EdYazbec/MotorCityField/2025 Specific/TE-25100/TE-25100.SLDASM

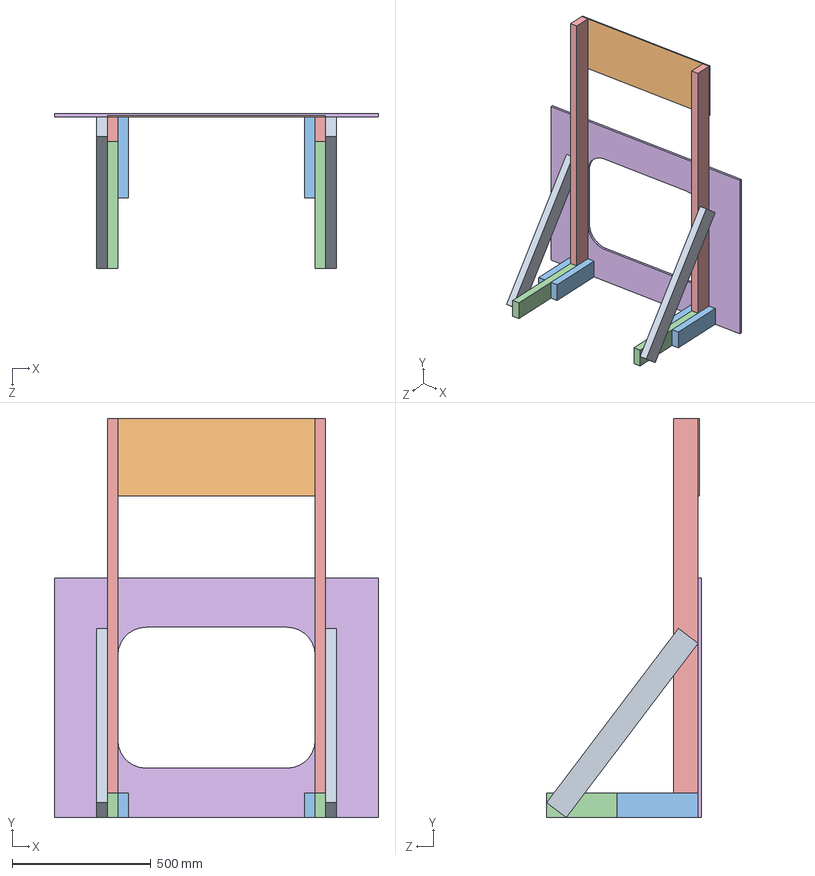
[picture p19: CAD file, 2025-06-08]
2025 Specific/TE-25100/TE-25100.SLDASM
1168.4 x 1438.3 x 558.0 mm
TE-25101
TE-25102 x 2
TE-25103 x 2
TE-25105 x 4
TE-25106
TE-25104 x 2
