EdYazbec/MotorCityField/Perimeter/Gate Segment/Gate Segment.SLDASM

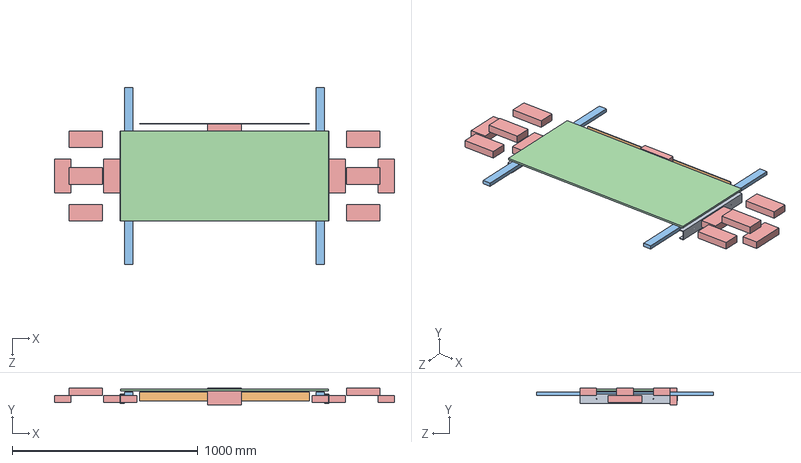
[picture p20: CAD file, 2025-06-08]
Perimeter/Gate Segment/Gate Segment.SLDASM
1828.8 x 88.9 x 952.5 mm
2x4 x 13
Gate Door Pannel
1x2 x 2
2in Hook Tape
u channel x 2
