EdYazbec/MotorCityField/Driver Station Wall/Driver Station/Driver Station.SLDASM

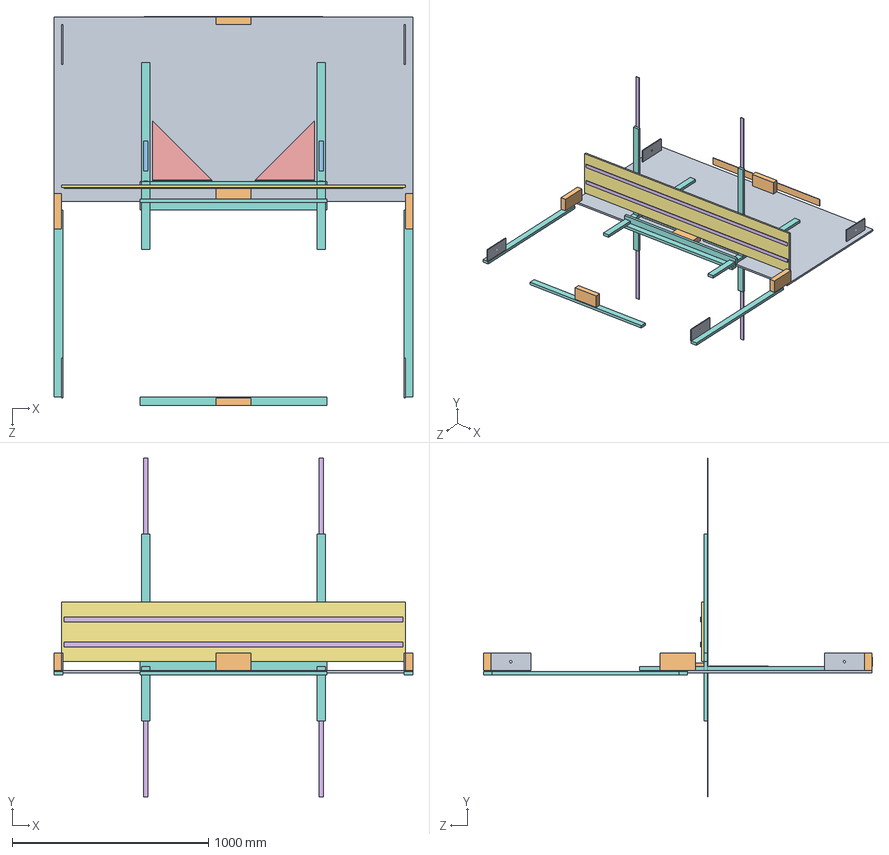
[picture p21: CAD file, 2025-06-08]
Driver Station Wall/Driver Station/Driver Station.SLDASM
1828.8 x 1727.2 x 1984.4 mm
2x4 x 5
DS Wall Plate
1x2 x 10
DS Shelf Slab
1in Hook Tape x 4
DS Shelf Support x 2
0.5in Loop Tape x 2
1in Loop Tape x 2
2in Hook Tape
DS Spacer x 4
