EdYazbec/MotorCityField/Driver Station Wall/Driver Station/DS Shelf.SLDASM

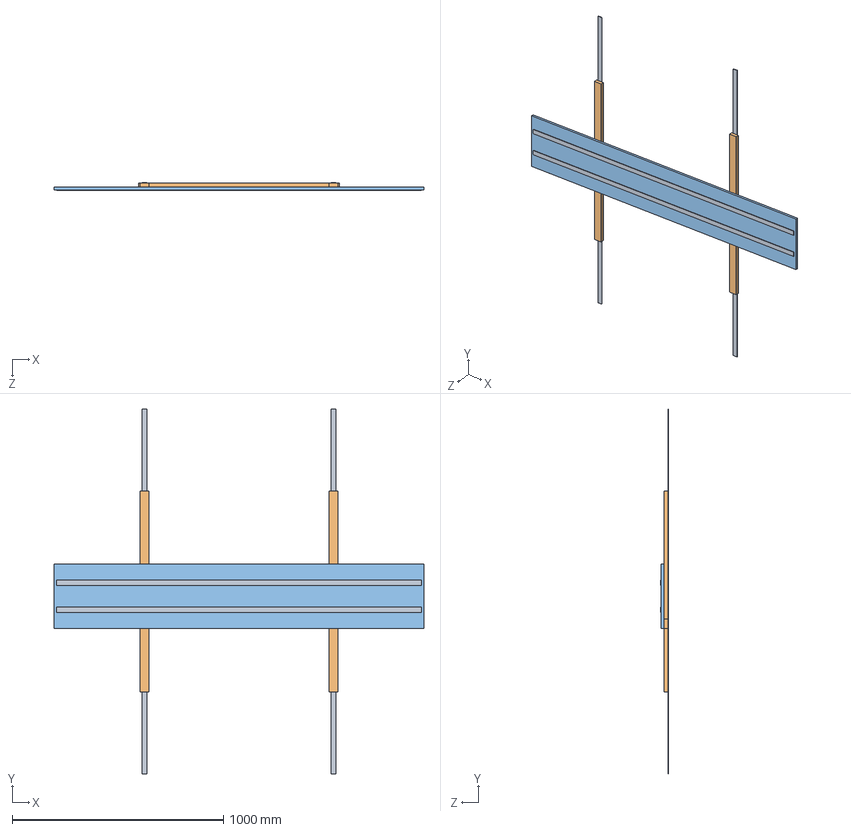
[picture p22: CAD file, 2025-06-08]
Driver Station Wall/Driver Station/DS Shelf.SLDASM
1752.6 x 1727.2 x 38.1 mm
DS Shelf Slab
1x2 x 3
1in Hook Tape x 4
