EdYazbec/MotorCityField/2025 Specific/TE-25100/TE-25103.SLDPRT

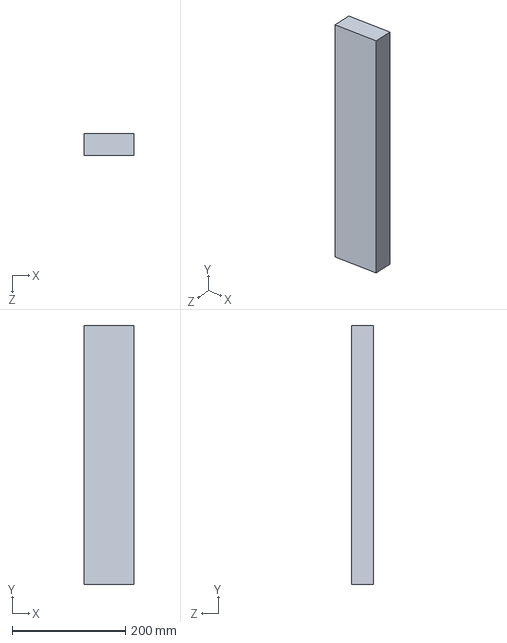
[picture p26: CAD file, 2025-06-08]
2025 Specific/TE-25100/TE-25103.SLDPRT
88.9 x 457.2 x 38.1 mm
