EdYazbec/MotorCityField/Common/1in Loop Tape.SLDPRT

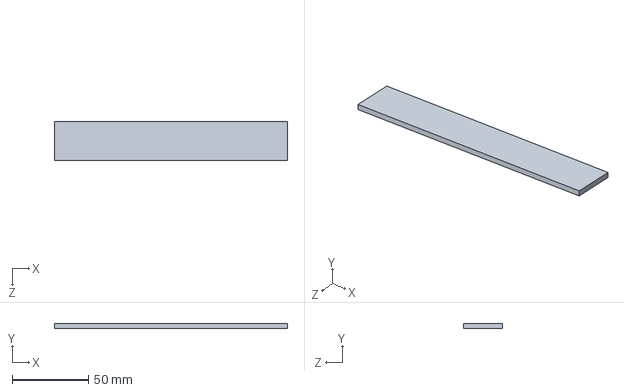
[picture p27: CAD file, 2025-06-08]
Common/1in Loop Tape.SLDPRT
152.4 x 3.17 x 25.4 mm
