EdYazbec/MotorCityField/Driver Station Wall/Driver Station Bace/DS Brace Bottom Fin.SLDPRT

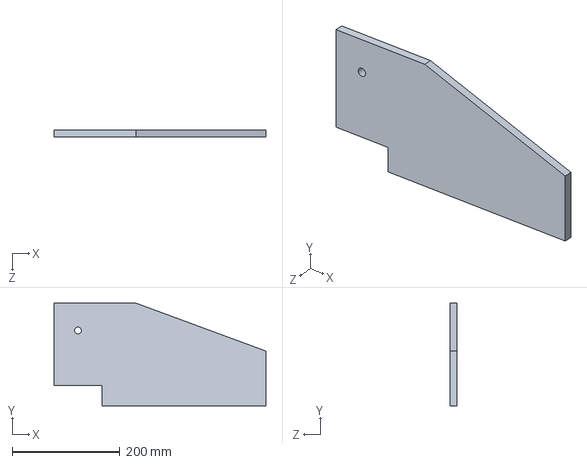
[picture p28: CAD file, 2025-06-08]
Driver Station Wall/Driver Station Bace/DS Brace Bottom Fin.SLDPRT
393.7 x 190.5 x 12.7 mm
