EdYazbec/MotorCityField/Perimeter/Gate Segment/Gate Door Pannel.SLDPRT

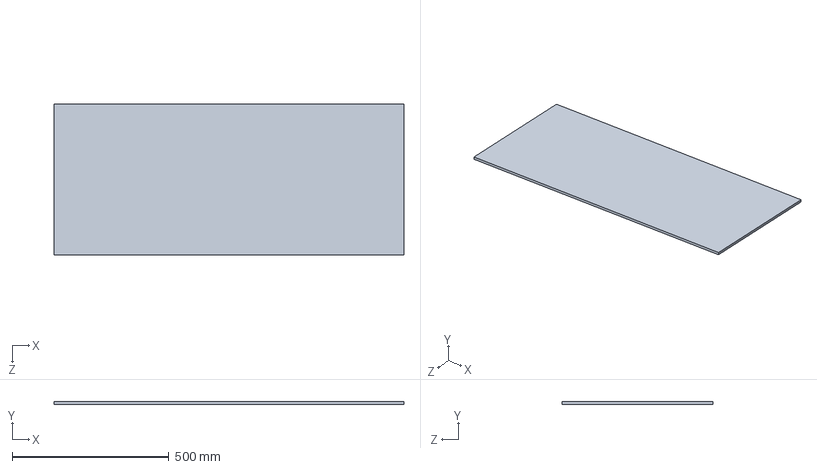
[picture p29: CAD file, 2025-06-08]
Perimeter/Gate Segment/Gate Door Pannel.SLDPRT
1117.6 x 9.53 x 482.6 mm
