EdYazbec/MotorCityField/Perimeter/Perimeter Brace/Wall gusset.SLDPRT

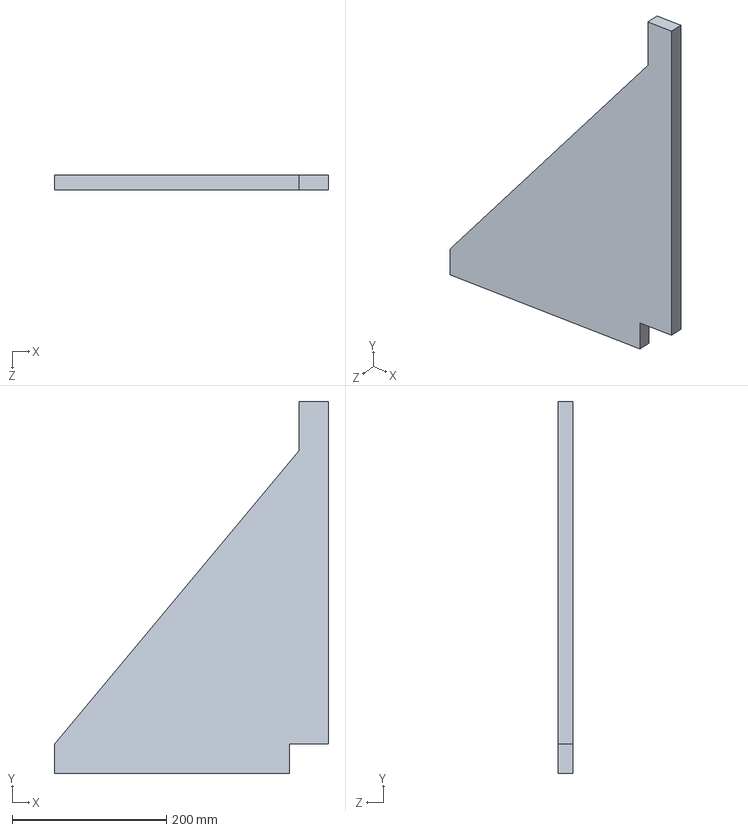
[picture p30: CAD file, 2025-06-08]
Perimeter/Perimeter Brace/Wall gusset.SLDPRT
355.6 x 482.6 x 19.1 mm
