EdYazbec/MotorCityField/2025 Specific/TE-25100/TE-25105.SLDPRT

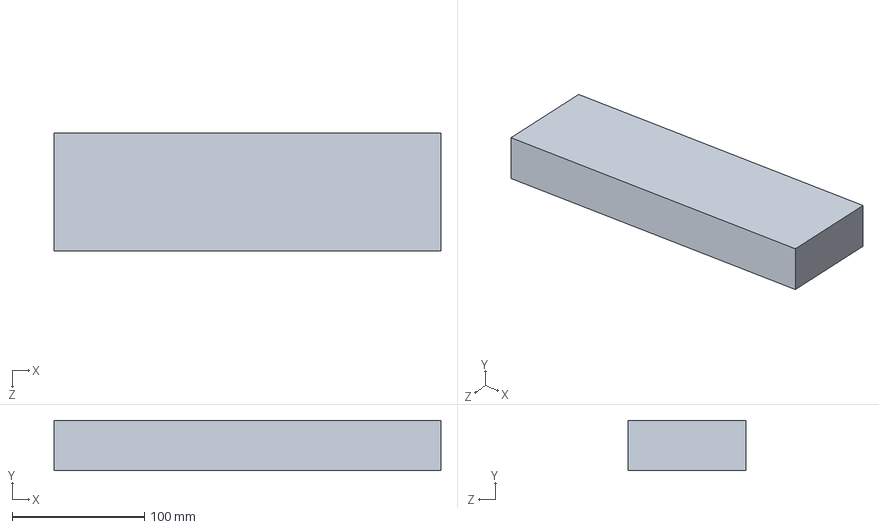
[picture p31: CAD file, 2025-06-08]
2025 Specific/TE-25100/TE-25105.SLDPRT
292.1 x 38.1 x 88.9 mm
