EdYazbec/MotorCityField/Common/0.5in Loop Tape.SLDPRT

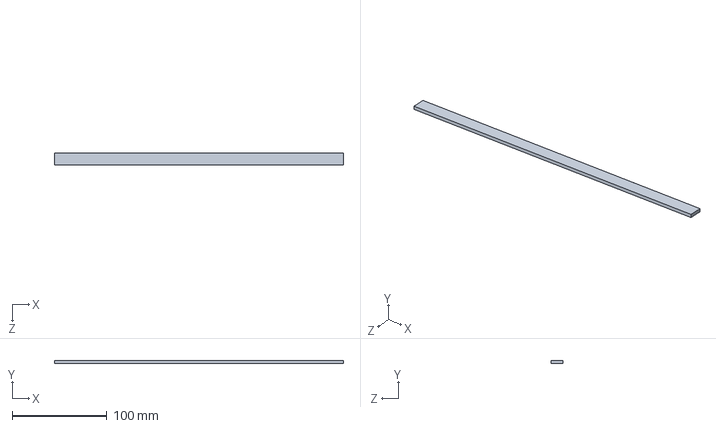
[picture p32: CAD file, 2025-06-08]
Common/0.5in Loop Tape.SLDPRT
304.8 x 3.17 x 12.7 mm
