EdYazbec/MotorCityField/Driver Station Wall/Driver Station Bace/DS Brace Top Fin.SLDPRT

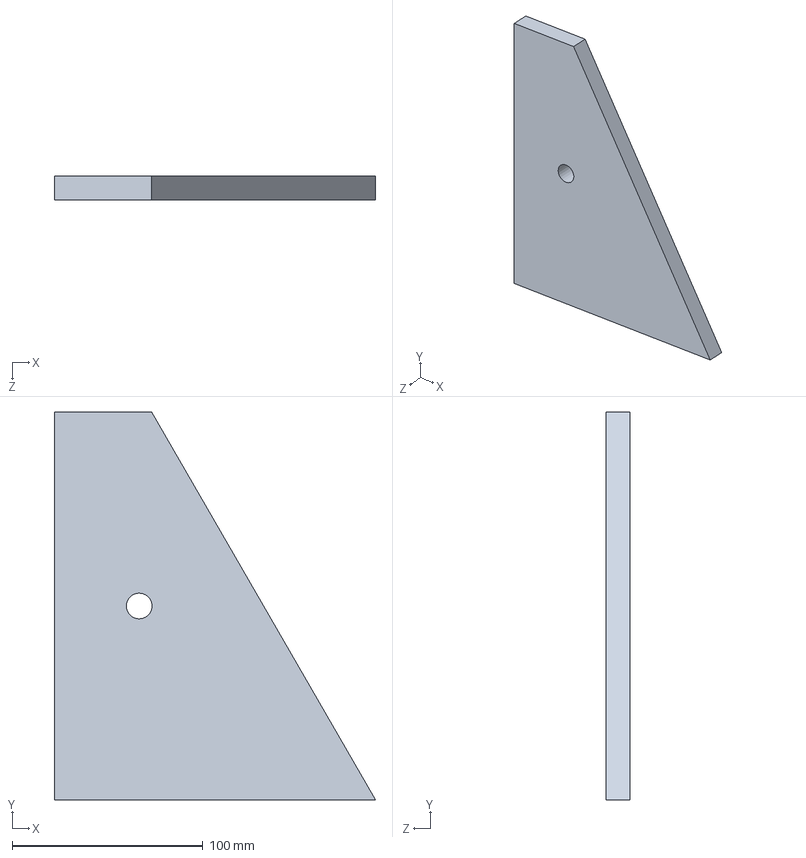
[picture p33: CAD file, 2025-06-08]
Driver Station Wall/Driver Station Bace/DS Brace Top Fin.SLDPRT
168.3 x 203.2 x 12.7 mm
