EdYazbec/MotorCityField/Driver Station Wall/Driver Station/DS Spacer.SLDPRT

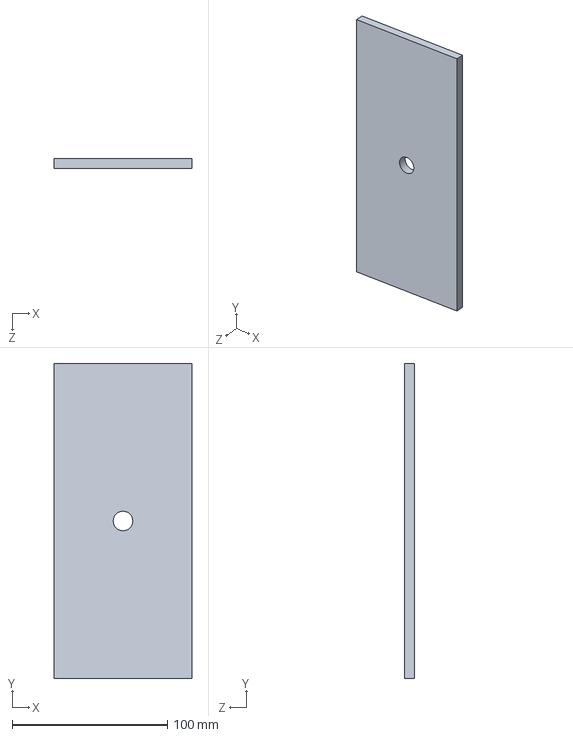
[picture p34: CAD file, 2025-06-08]
Driver Station Wall/Driver Station/DS Spacer.SLDPRT
88.9 x 203.2 x 6.35 mm
