EdYazbec/MotorCityField/Perimeter/Gate Segment/u channel.SLDPRT

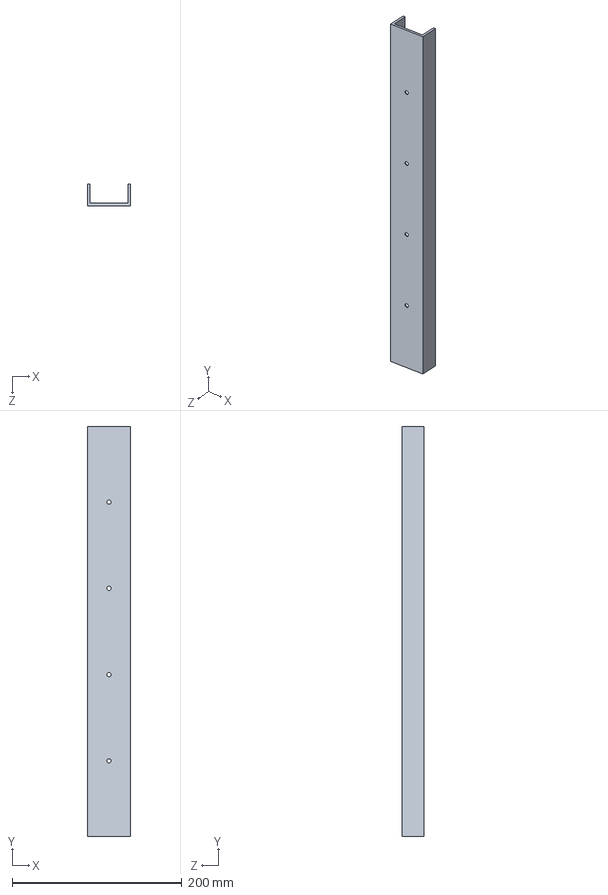
[picture p35: CAD file, 2025-06-08]
Perimeter/Gate Segment/u channel.SLDPRT
50.8 x 482.6 x 25.4 mm
