EdYazbec/MotorCityField/Common/2x4.SLDPRT

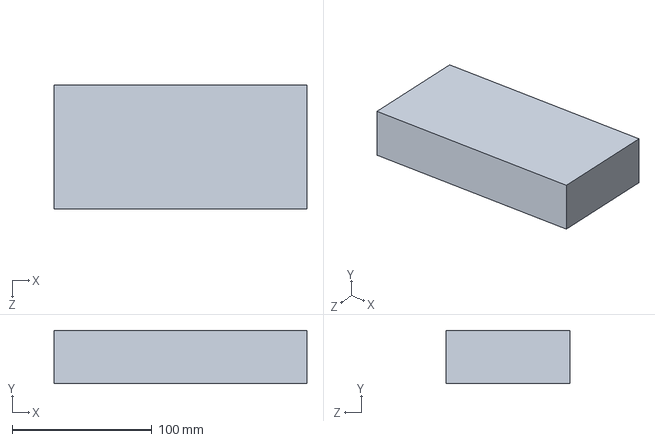
[picture p36: CAD file, 2025-06-08]
Common/2x4.SLDPRT
181.0 x 38.1 x 88.9 mm
