EdYazbec/MotorCityField/Driver Station Wall/Driver Station Bace/2x4 DS angled piece.SLDPRT

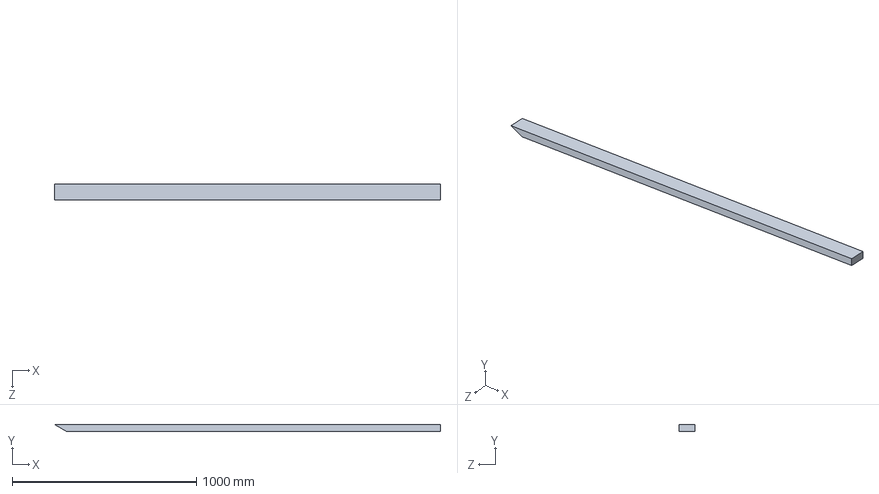
[picture p37: CAD file, 2025-06-08]
Driver Station Wall/Driver Station Bace/2x4 DS angled piece.SLDPRT
2095.5 x 38.1 x 88.9 mm
