EdYazbec/MotorCityField/Driver Station Wall/Driver Station/DS Shelf Support.SLDPRT

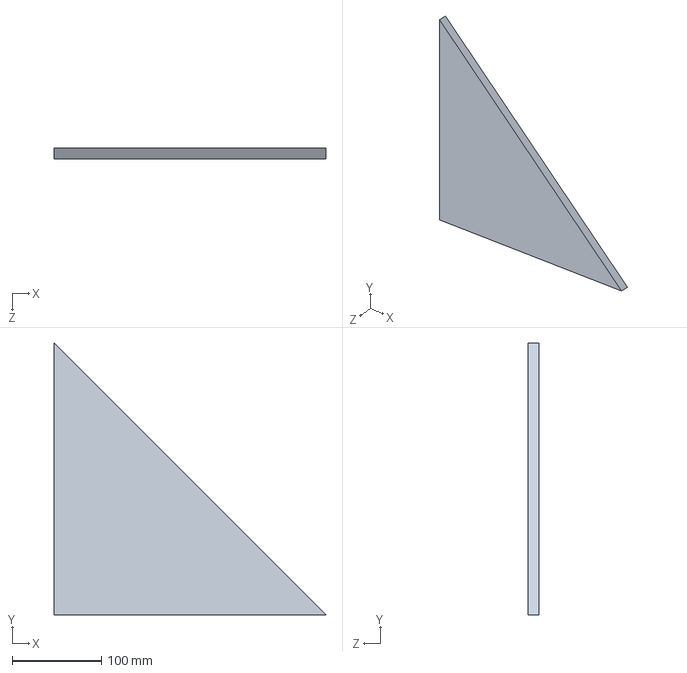
[picture p38: CAD file, 2025-06-08]
Driver Station Wall/Driver Station/DS Shelf Support.SLDPRT
304.8 x 304.8 x 12.7 mm
