EdYazbec/MotorCityField/2025 Specific/TE-25100/TE-25101.SLDPRT

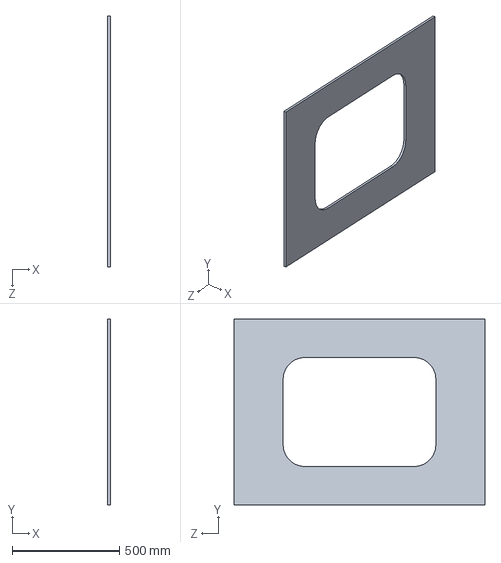
[picture p39: CAD file, 2025-06-08]
2025 Specific/TE-25100/TE-25101.SLDPRT
11.9 x 863.6 x 1168.4 mm
