EdYazbec/MotorCityField/Common/2in Hook Tape.SLDPRT

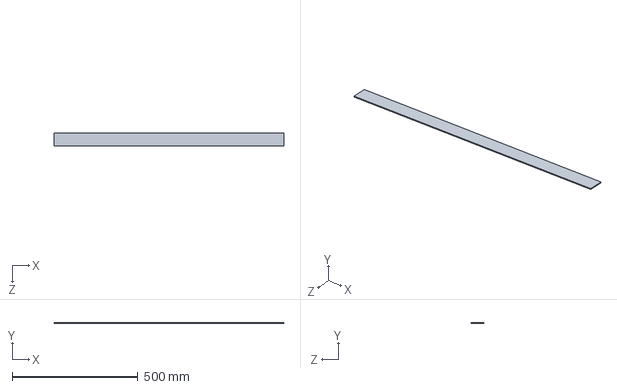
[picture p40: CAD file, 2025-06-08]
Common/2in Hook Tape.SLDPRT
914.4 x 3.17 x 50.8 mm
