EdYazbec/MotorCityField/Driver Station Wall/Driver Station/DS Wall Wedge.SLDPRT

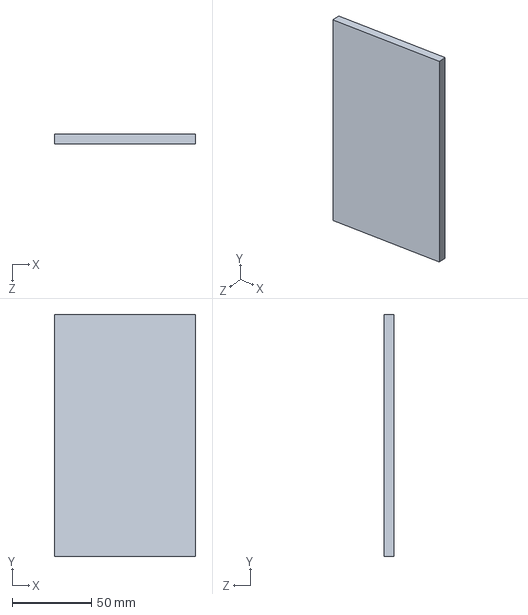
[picture p41: CAD file, 2025-06-08]
Driver Station Wall/Driver Station/DS Wall Wedge.SLDPRT
88.9 x 152.4 x 6.35 mm
