EdYazbec/MotorCityField/2025 Specific/TE-25100/TE-25102.SLDPRT

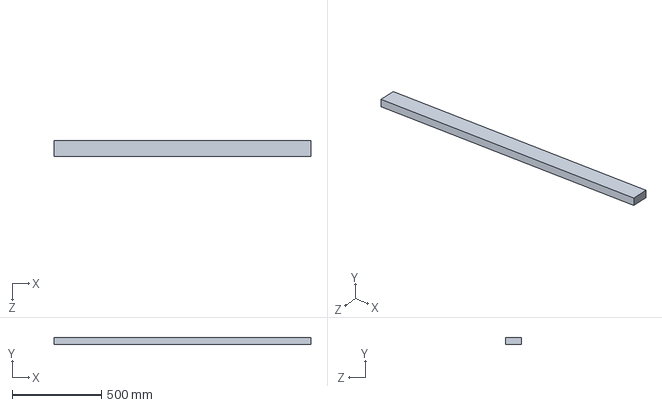
[picture p42: CAD file, 2025-06-08]
2025 Specific/TE-25100/TE-25102.SLDPRT
1438.3 x 38.1 x 88.9 mm
