EdYazbec/MotorCityField/Common/1x2.SLDPRT

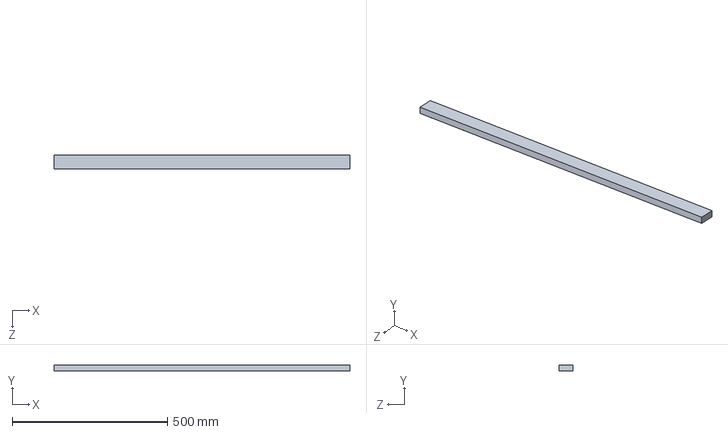
[picture p43: CAD file, 2025-06-08]
Common/1x2.SLDPRT
952.5 x 19.1 x 44.5 mm
