EdYazbec/MotorCityField/2025 Specific/TE-25100/TE-25104.SLDPRT

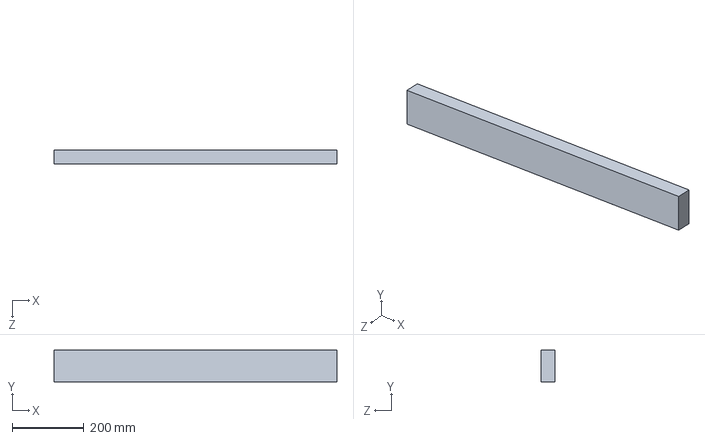
[picture p44: CAD file, 2025-06-08]
2025 Specific/TE-25100/TE-25104.SLDPRT
787.4 x 88.9 x 38.1 mm
