EdYazbec/MotorCityField/Driver Station Wall/Driver Station/DS Wall Plate.SLDPRT

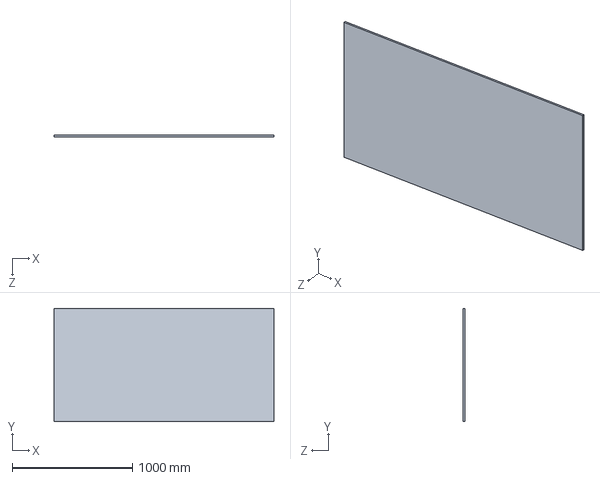
[picture p45: CAD file, 2025-06-08]
Driver Station Wall/Driver Station/DS Wall Plate.SLDPRT
1828.8 x 939.8 x 12.7 mm
