EdYazbec/MotorCityField/Driver Station Wall/Driver Station/DS Shelf Slab.SLDPRT

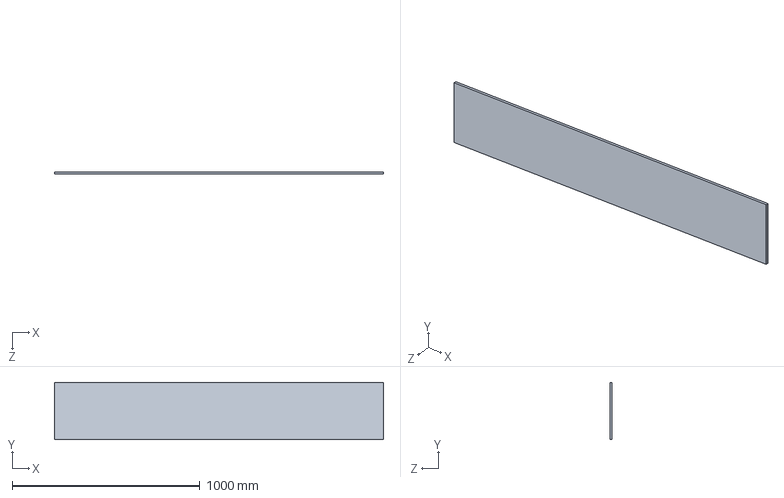
[picture p46: CAD file, 2025-06-08]
Driver Station Wall/Driver Station/DS Shelf Slab.SLDPRT
1752.6 x 304.8 x 12.7 mm
