EdYazbec/MotorCityField/Drawing Package/Driver Station Wall/Driver Station/DS Shelf Support LH.pdf

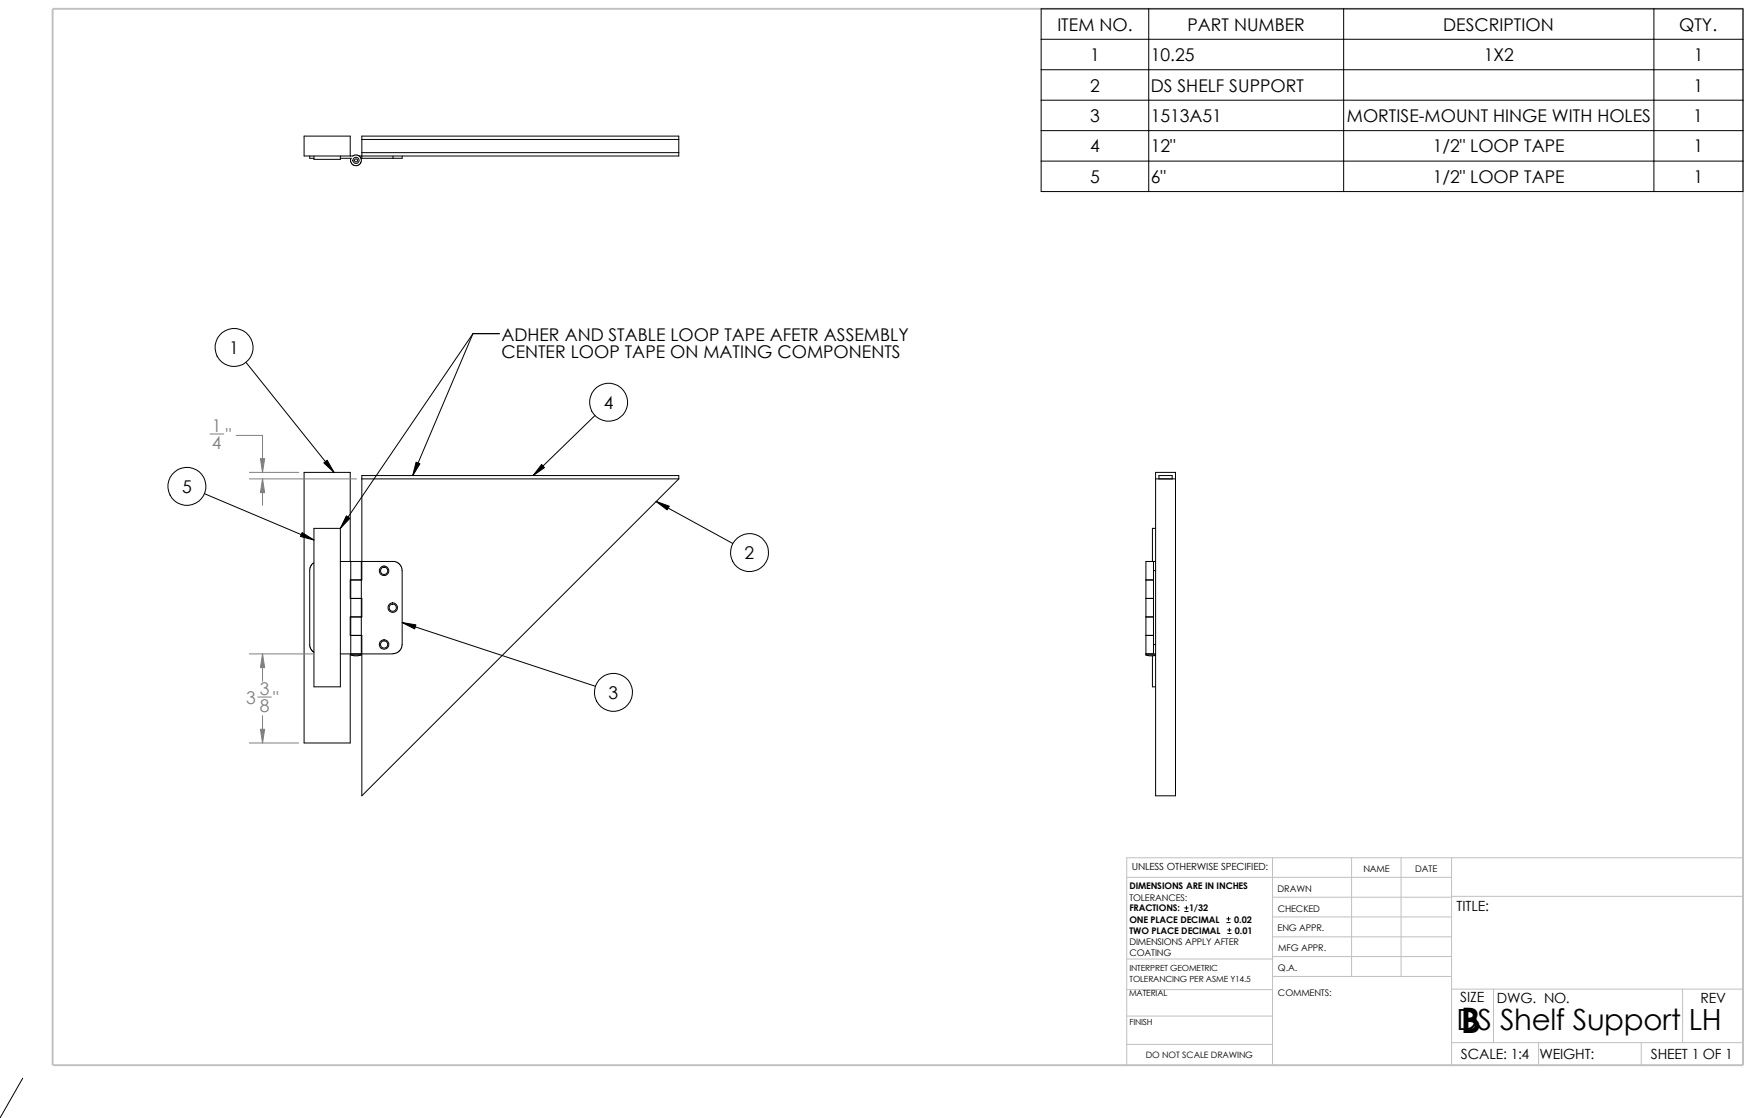
[picture p57: page 1]
COMMENTS:; DWG. NO.; REV; SCALE: 1:4; WEIGHT:; SIZE; FINISH; DS Shelf Support LH B; MATERIAL; SHEET 1 OF 1

ITEM NO. | PART NUMBER | DESCRIPTION | QTY.
1 | 10.25 | 1X2 | 1
2 | DS SHELF SUPPORT | | 1
3 | 1513A51 | MORTISE-MOUNT HINGE WITH HOLES | 1
4 | 12" | 1/2" LOOP TAPE | 1
5 | 6" | 1/2" LOOP TAPE | 1

ADHER AND STABLE LOOP TAPE AFETR ASSEMBLY
CENTER LOOP TAPE ON MATING COMPONENTS

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

CHECKED | | | TITLE:

ENG APPR.
MFG APPR.

INTERPRET GEOMETRIC TOLERANCING PER ASME Y14.5 | Q.A.

DO NOT SCALE DRAWING
