EdYazbec/MotorCityField/Drawing Package/Driver Station Wall/Driver Station/DS Shelf.pdf

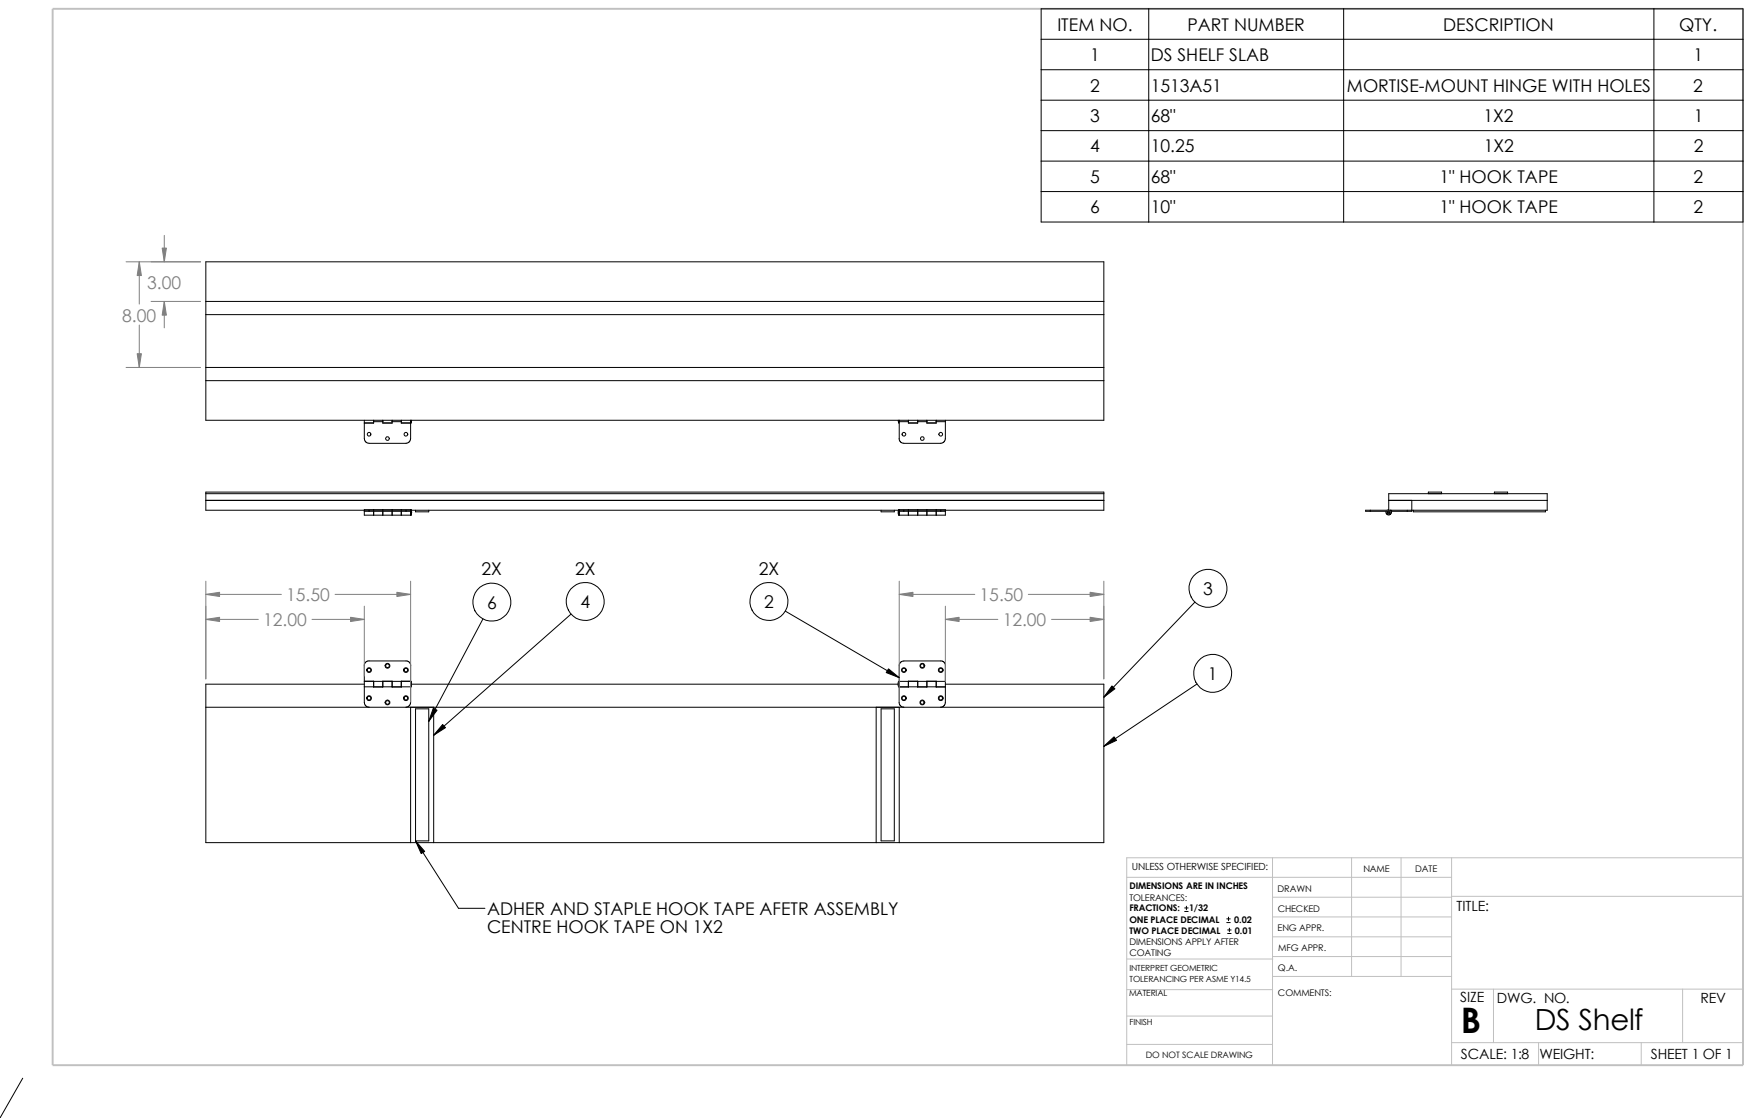
[picture p58: page 1]
COMMENTS:; DS Shelf; REV; WEIGHT:; SIZE; DWG. NO.; SCALE: 1:8; FINISH; MATERIAL; SHEET 1 OF 1

ITEM NO. | PART NUMBER | DESCRIPTION | QTY.
1 | DS SHELF SLAB | | 1
2 | 1513A51 | MORTISE-MOUNT HINGE WITH HOLES | 2
3 | 68" | 1X2 | 1
4 | 10.25 | 1X2 | 2
5 | 68" | 1" HOOK TAPE | 2
6 | 10" | 1" HOOK TAPE | 2

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

ADHER AND STAPLE HOOK TAPE AFETR ASSEMBLY
CENTRE HOOK TAPE ON 1X2

CHECKED | | | TITLE:

ENG APPR.
MFG APPR.

INTERPRET GEOMETRIC TOLERANCING PER ASME Y14.5 | Q.A.

DO NOT SCALE DRAWING
