EdYazbec/MotorCityField/Drawing Package/Driver Station Wall/Driver Station/DS Spacer.pdf

1
4

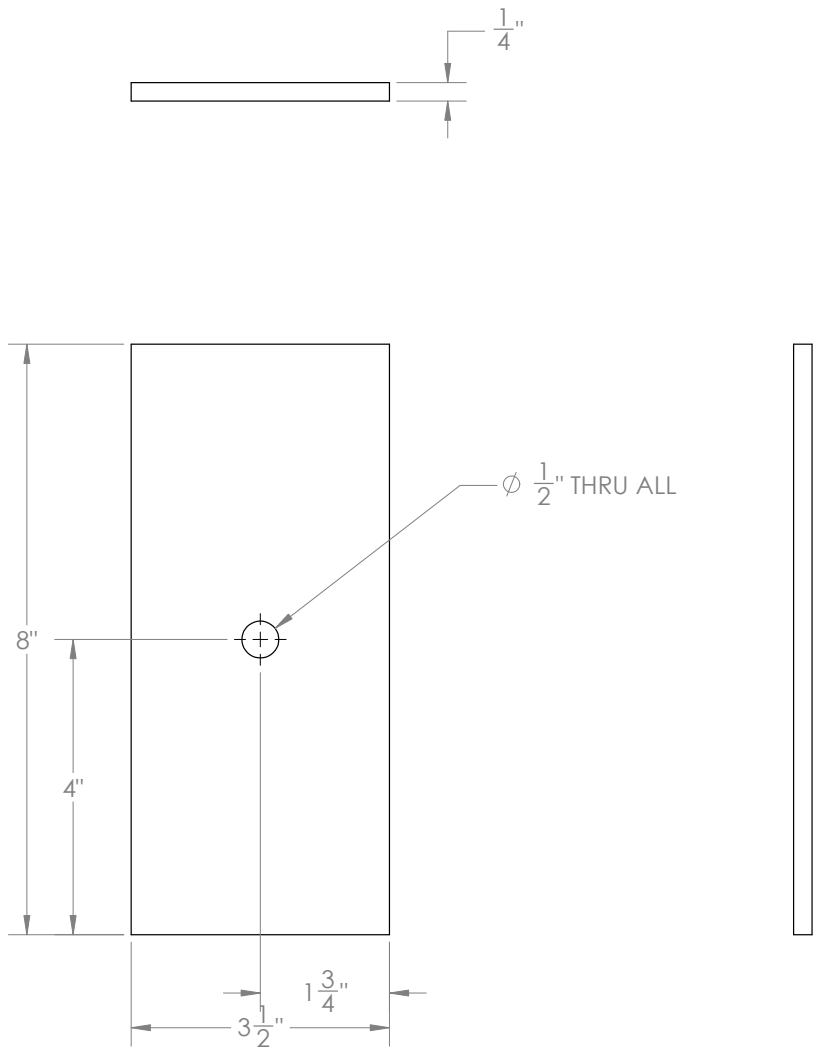
[picture p59: page 1]
SIZE; REV; COMMENTS:; DS Spacer; FINISH; SHEET 1 OF 1; SCALE: 1:2; WEIGHT:; " THRU ALL

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

CHECKED | | | TITLE:

ENG APPR.
MFG APPR.

INTERPRET GEOMETRIC TOLERANCING PER ASME Y14.5 | Q.A.

MATERIAL
DWG. NO. 1/4" PLYWOOD

DO NOT SCALE DRAWING
