EdYazbec/MotorCityField/Drawing Package/Driver Station Wall/Driver Station/DS Wall Plate.pdf

.50

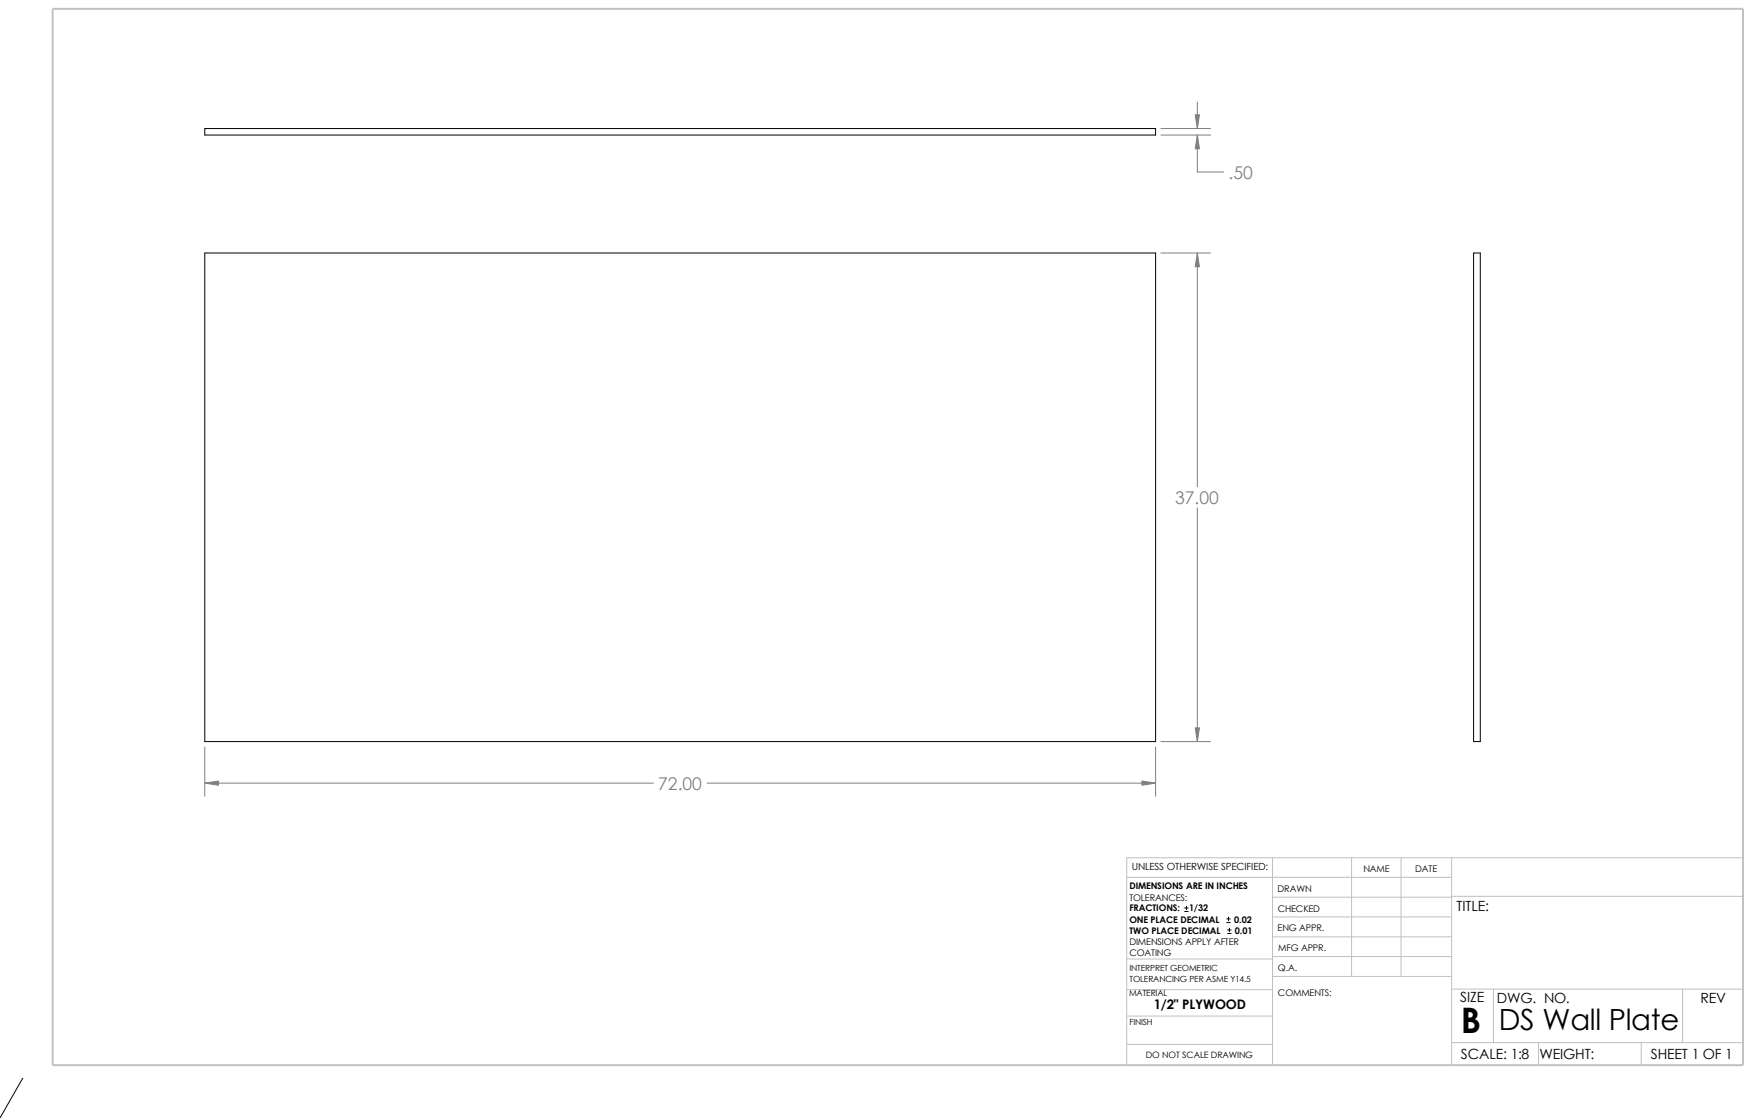
[picture p60: page 1]
SIZE; REV; COMMENTS:; FINISH; SHEET 1 OF 1; SCALE: 1:8; WEIGHT:

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

CHECKED | | | TITLE:

ENG APPR.
MFG APPR.

INTERPRET GEOMETRIC TOLERANCING PER ASME Y14.5 | Q.A.

MATERIAL
DWG. NO. 1/2" PLYWOOD

DS Wall Plate

DO NOT SCALE DRAWING
