EdYazbec/MotorCityField/Drawing Package/Perimeter/Gate Segment/Gate Door.pdf

2 2X

3 2X | ITEM NO. | PART / LENGTH | MATERIAL | QTY.

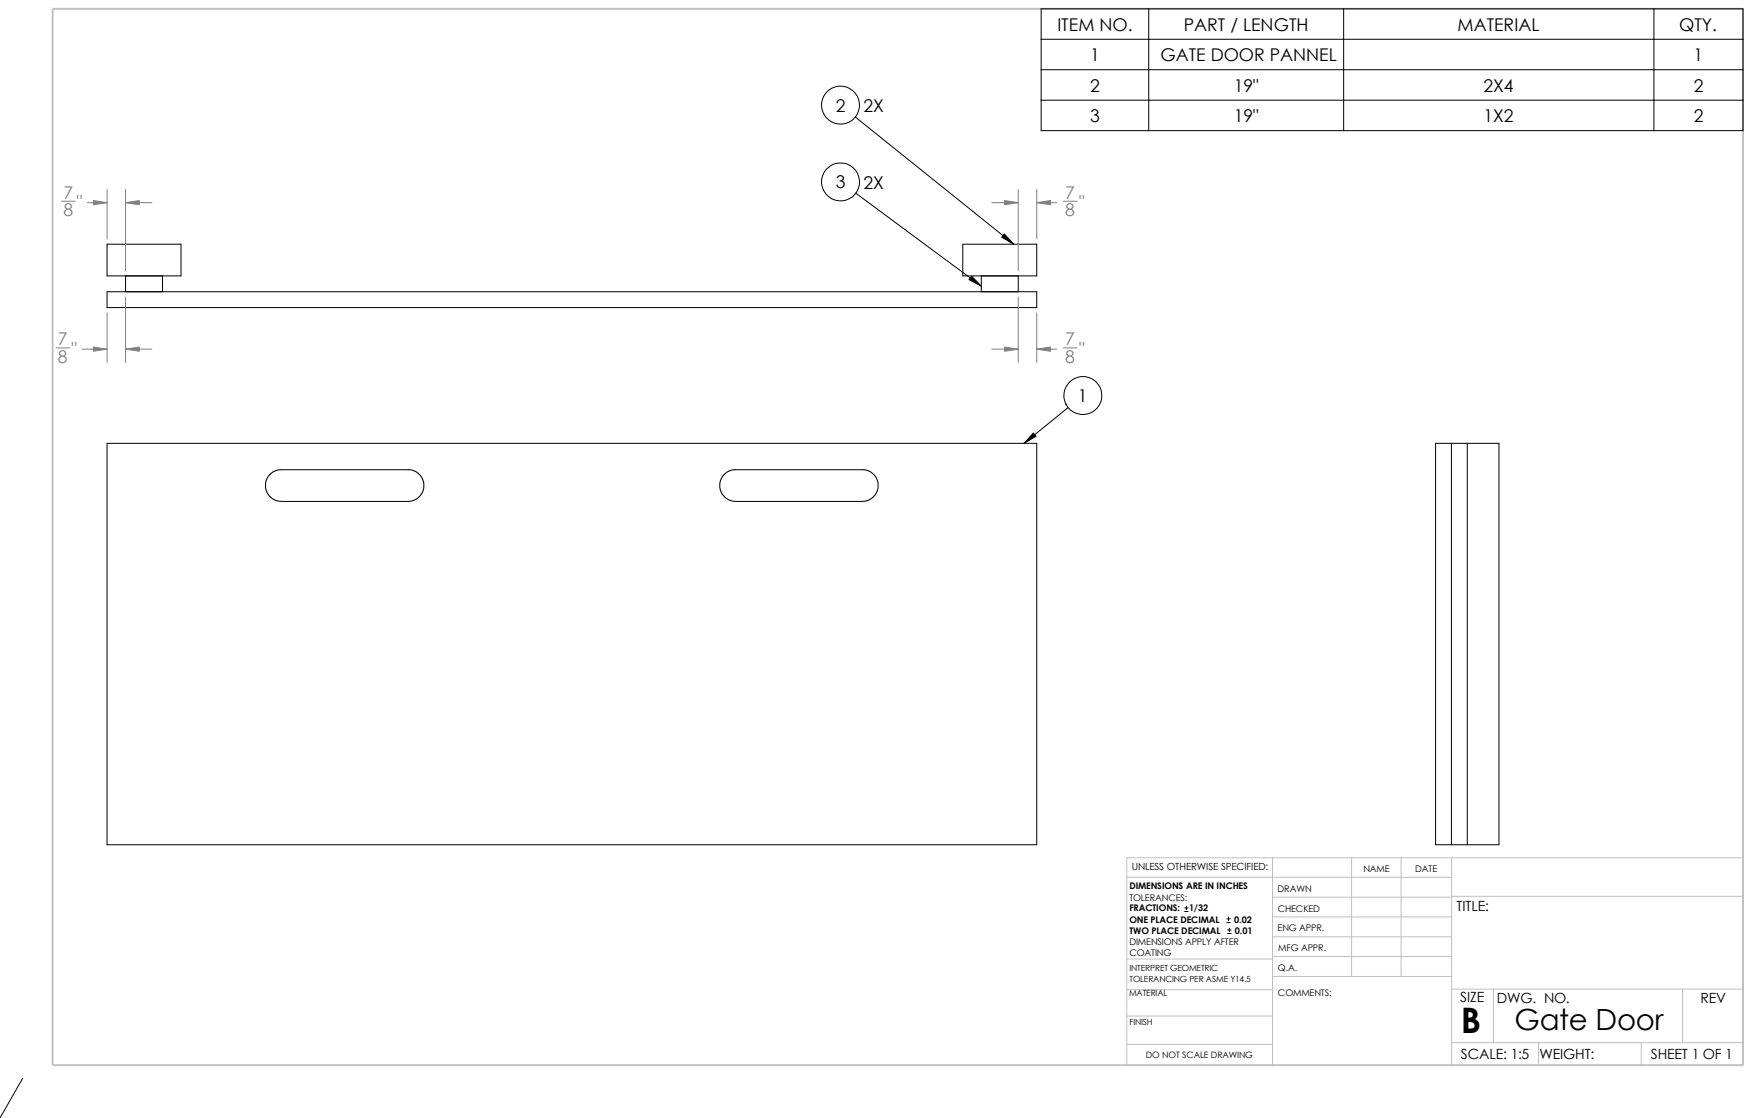
[picture p61: page 1]
COMMENTS:; DWG. NO.; REV; SCALE: 1:5; WEIGHT:; SIZE; SHEET 1 OF 1

1 | GATE DOOR PANNEL | | 1
2 | 19" | 2X4 | 2
3 | 19" | 1X2 | 2

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

CHECKED | | | TITLE:

ENG APPR.
MFG APPR.

INTERPRET GEOMETRIC TOLERANCING PER ASME Y14.5 | Q.A.

MATERIAL
B Gate Door FINISH

DO NOT SCALE DRAWING
