EdYazbec/MotorCityField/Drawing Package/Perimeter/Gate Segment/Gate Segment.pdf

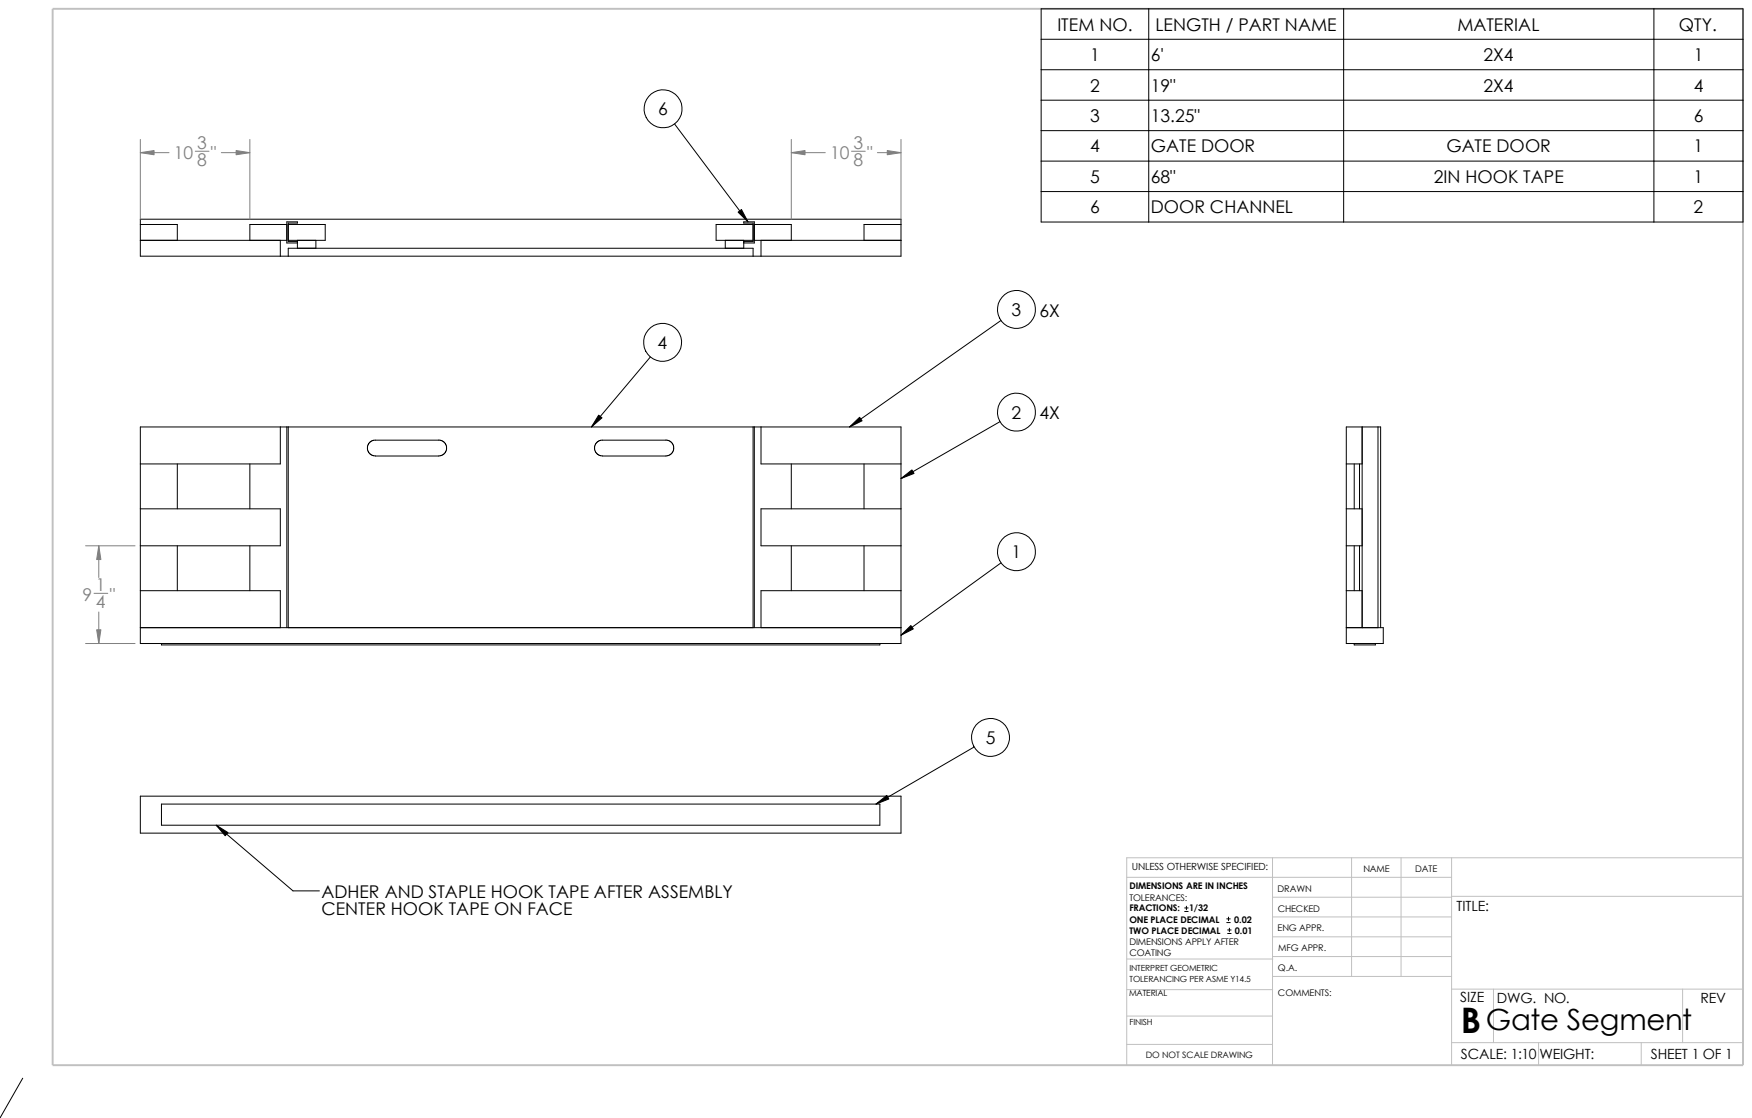
[picture p62: page 1]
COMMENTS:; DWG. NO.; REV; SCALE: 1:10 WEIGHT:; SIZE; SHEET 1 OF 1

6 | ITEM NO. | LENGTH / PART NAME | MATERIAL | QTY.

1 | 6' | 2X4 | 1
2 | 19" | 2X4 | 4
3 | 13.25" | | 6
4 | GATE DOOR | GATE DOOR | 1
5 | 68" | 2IN HOOK TAPE | 1
6 | DOOR CHANNEL | | 2

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

ADHER AND STAPLE HOOK TAPE AFTER ASSEMBLY
CENTER HOOK TAPE ON FACE

CHECKED | | | TITLE:

ENG APPR.
MFG APPR.

INTERPRET GEOMETRIC TOLERANCING PER ASME Y14.5 | Q.A.

MATERIAL
B Gate Segment FINISH

DO NOT SCALE DRAWING
