EdYazbec/MotorCityField/Drawing Package/Perimeter/Wall Segment/Wall Segment.pdf

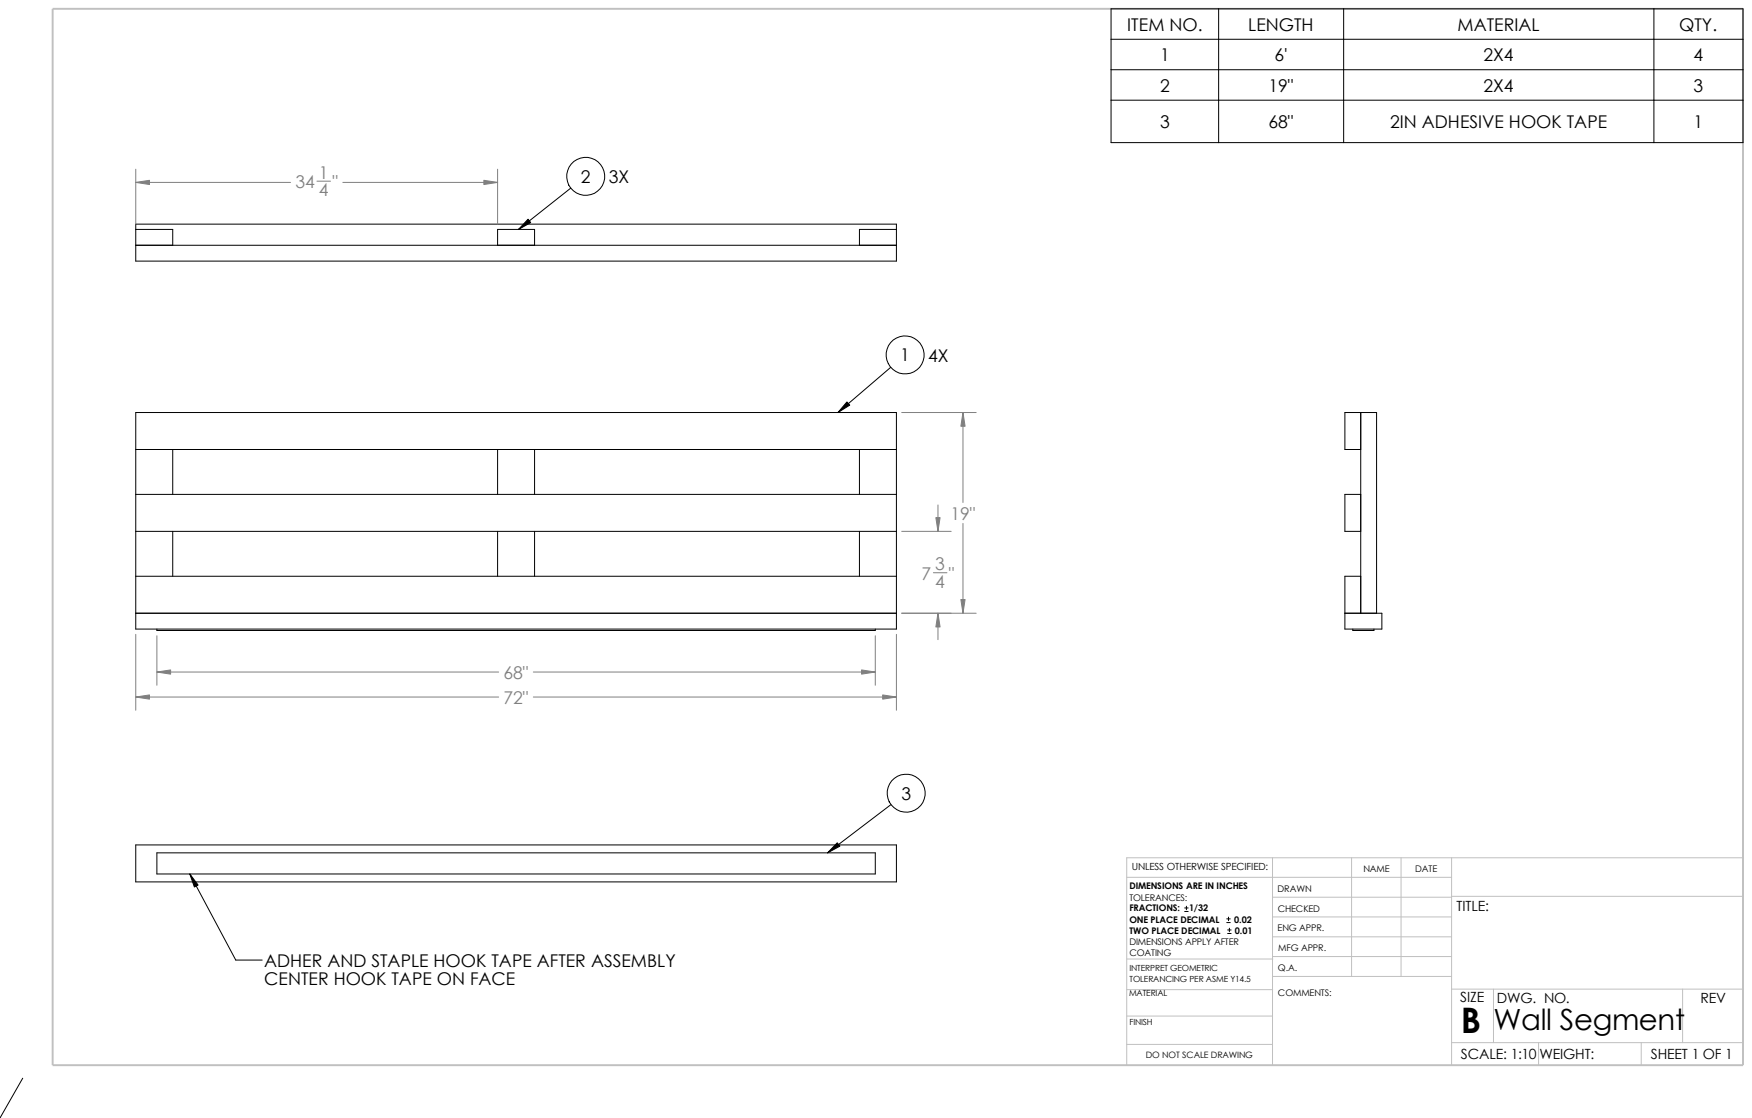
[picture p63: page 1]
COMMENTS:; DWG. NO.; REV; SCALE: 1:10 WEIGHT:; SIZE; SHEET 1 OF 1

ITEM NO. | LENGTH | MATERIAL | QTY.
1 | 6' | 2X4 | 4
2 | 19" | 2X4 | 3
3 | 68" | 2IN ADHESIVE HOOK TAPE | 1

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

CHECKED | | | TITLE:

ENG APPR.
MFG APPR.

ADHER AND STAPLE HOOK TAPE AFTER ASSEMBLY
CENTER HOOK TAPE ON FACE

INTERPRET GEOMETRIC TOLERANCING PER ASME Y14.5 | Q.A.

MATERIAL
B Wall Segment FINISH

DO NOT SCALE DRAWING
