EdYazbec/MotorCityField/Drawing Package/Driver Station Wall/Driver Station/DS Shelf Support.pdf

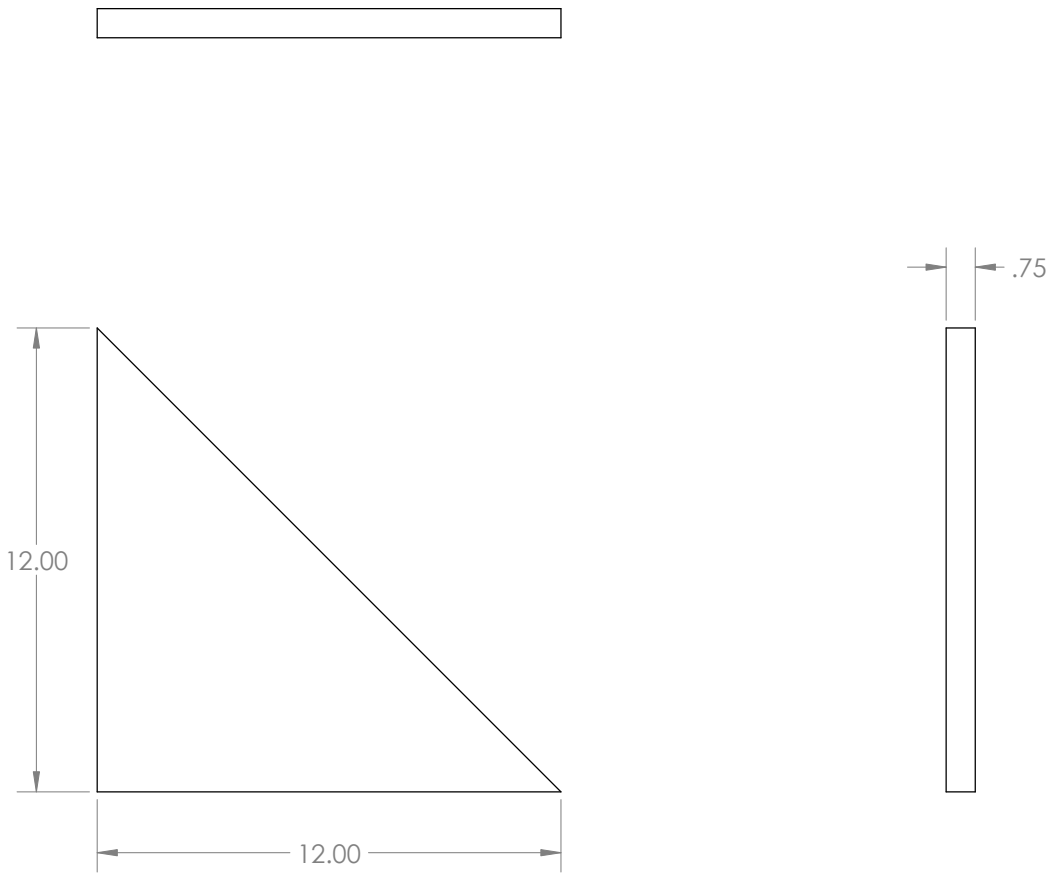
[picture p67: page 1]
WEIGHT:; COMMENTS:; SCALE: 1:4; 3/4" Plywood; SIZE; REV; MATERIAL; FINISH; SHEET 1 OF 1

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

CHECKED | | | TITLE:

ENG APPR.
MFG APPR.

INTERPRET GEOMETRIC TOLERANCING PER ASME Y14.5 | Q.A.

DWG. NO.
DS Shelf Support

DO NOT SCALE DRAWING
