EdYazbec/MotorCityField/Drawing Package/Perimeter/Gate Segment/Gate Door Pannel.pdf

8 1

" 4

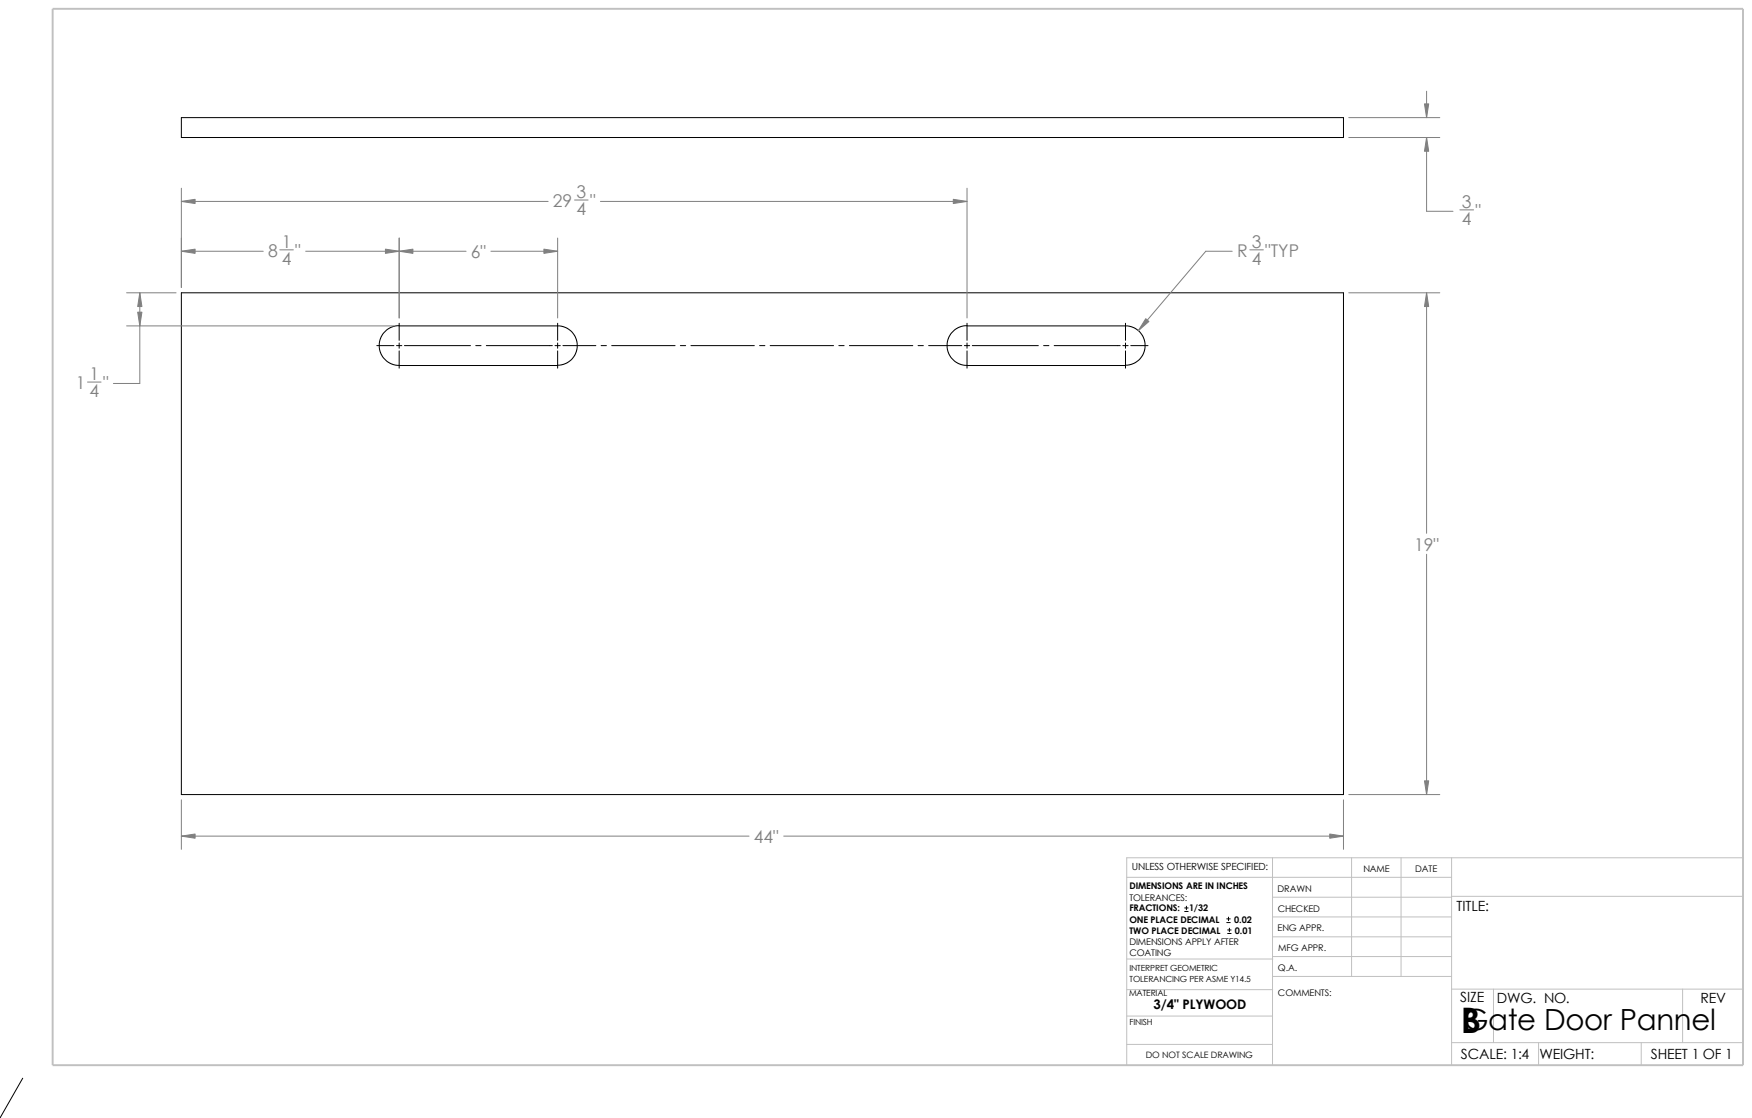
[picture p68: page 1]
SIZE; REV; COMMENTS:; FINISH; SHEET 1 OF 1; SCALE: 1:4; WEIGHT:; "TYP

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

CHECKED | | | TITLE:

ENG APPR.
MFG APPR.

INTERPRET GEOMETRIC TOLERANCING PER ASME Y14.5 | Q.A.

MATERIAL
DWG. NO. 3/4" PLYWOOD

Gate Door Pannel

DO NOT SCALE DRAWING
