EdYazbec/MotorCityField/Drawing Package/Perimeter/Gate Segment/u channel.pdf

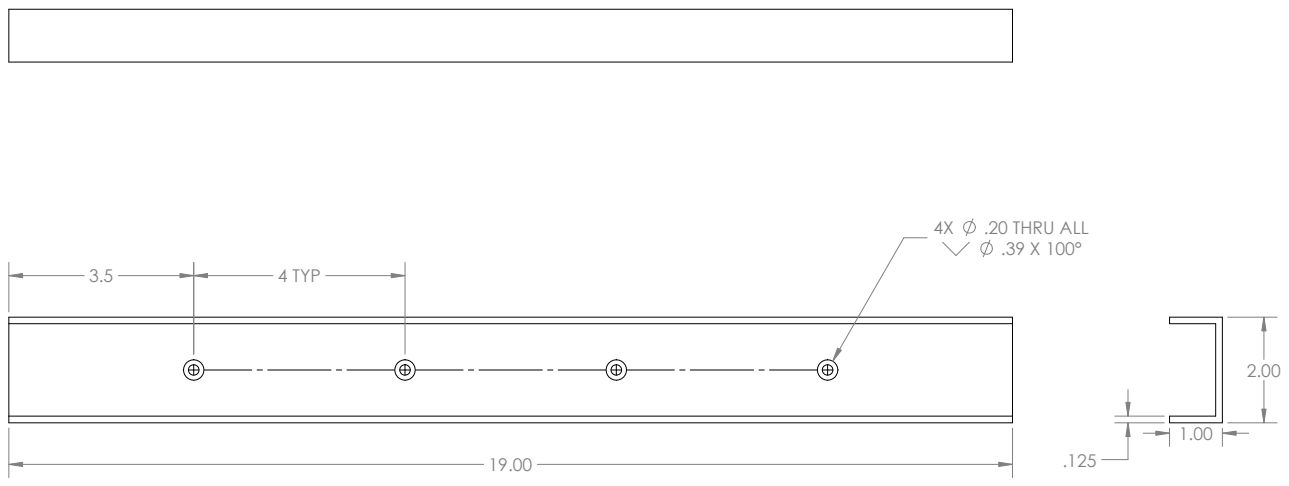
[picture p69: page 1]
SIZE; REV; COMMENTS:; u channel; FINISH; SHEET 1 OF 1; SCALE: 1:2; WEIGHT:; 4 TYP; .20 THRU ALL

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

CHECKED | | | TITLE:

ENG APPR.
MFG APPR.

INTERPRET GEOMETRIC TOLERANCING PER ASME Y14.5 | Q.A.

MATERIAL
DWG. NO. McMaster 9001K74

DO NOT SCALE DRAWING
