EdYazbec/MotorCityField/Drawing Package/Perimeter/Perimeter Brace/Perimeter Brace.pdf

ITEM NO. | PART / LENGTH | DESCRIPTION | QTY.
1 | 7.125" | 2X4 | 4

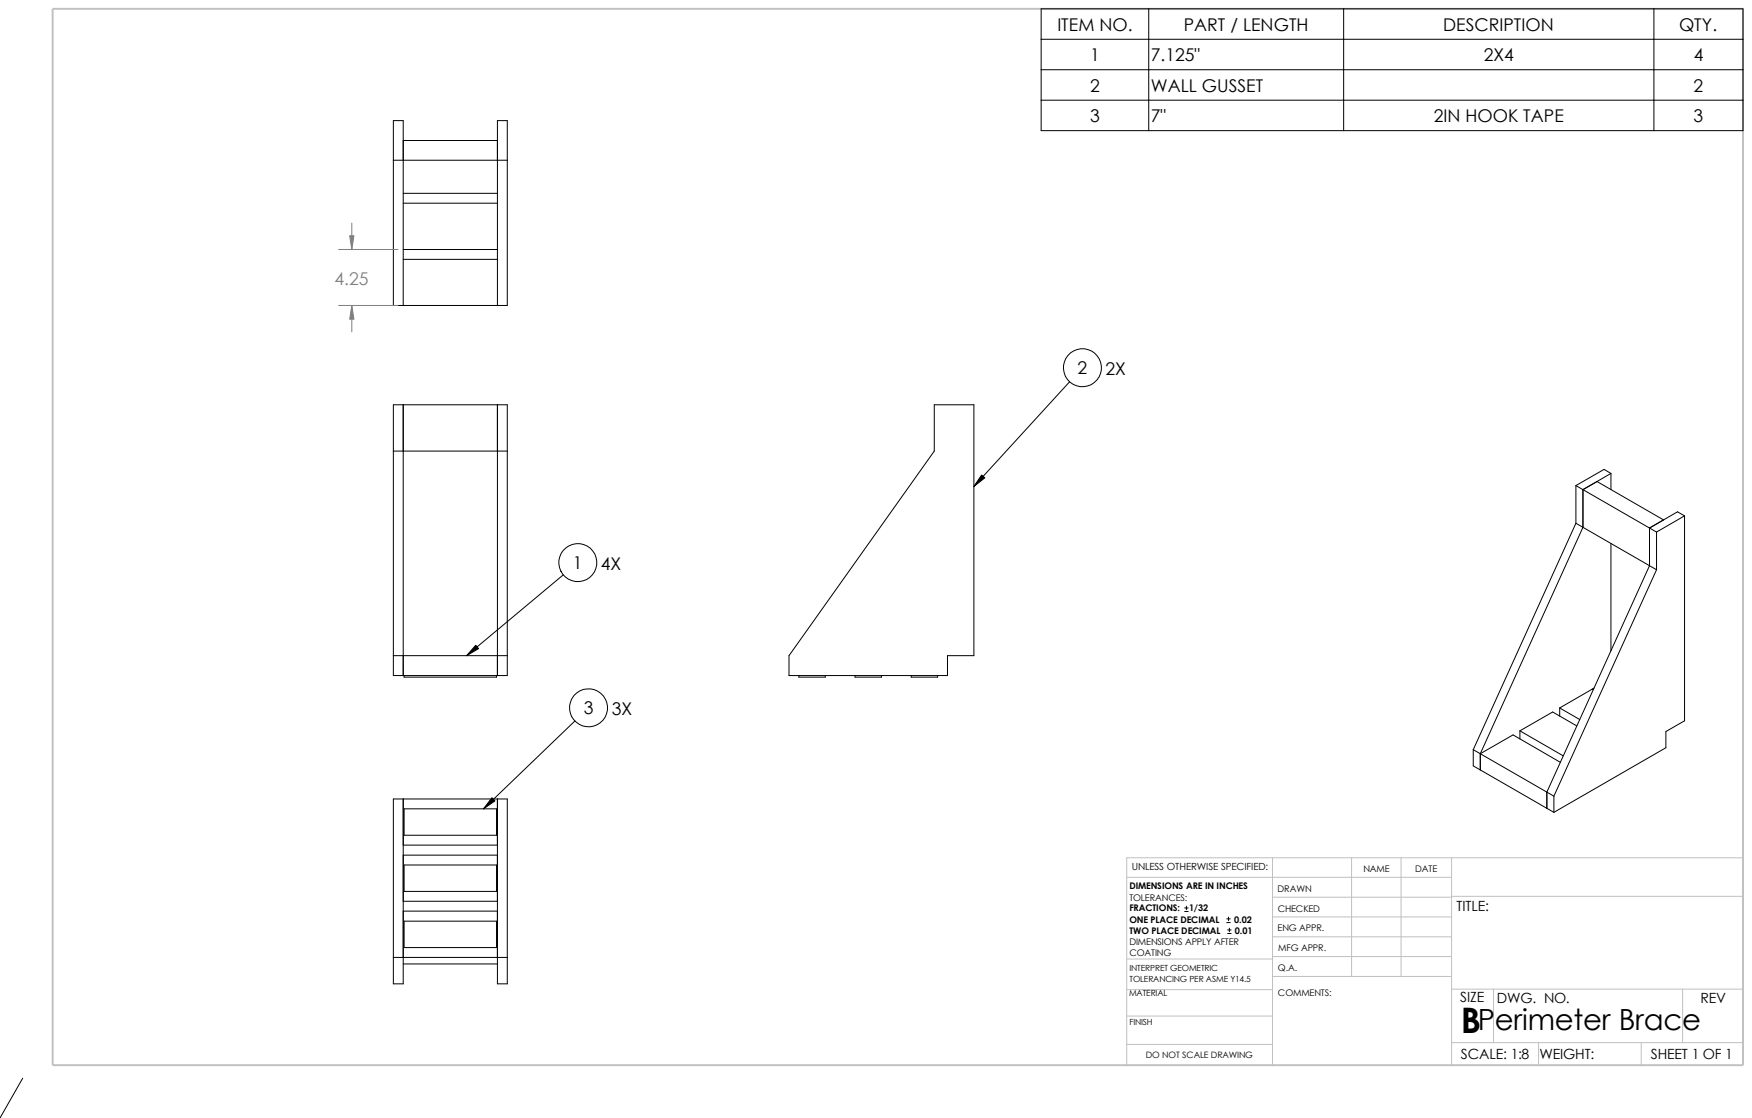
[picture p70: page 1]
COMMENTS:; DWG. NO.; REV; SCALE: 1:8; WEIGHT:; SIZE; FINISH; BPerimeter Brace; MATERIAL; SHEET 1 OF 1

2 | WALL GUSSET | | 2
3 | 7" | 2IN HOOK TAPE | 3

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

CHECKED | | | TITLE:

ENG APPR.
MFG APPR.

INTERPRET GEOMETRIC TOLERANCING PER ASME Y14.5 | Q.A.

DO NOT SCALE DRAWING
